tproffen/ORCSpilomar/circuitpython/tiny2350-tmc2209/pilomar/helpers.py

# Based on https://github.com/Short-bus/pilomar
# Simplified for use with TINY2350

import board
import digitalio
import time
import gc

#-----------------------------------------------------------------------------------------------
class GPIOpin():

    PinList = [] # Maintain a list of all defined pins.

    def __init__(self,pin,name=None):
        print("GPIOpin: Initializing pin",pin,name)
        self.Pin = digitalio.DigitalInOut(pin)
        self.PinNumber = pin
        self.Name = name
        self.PrevValue = self.GetValue()
        GPIOpin.PinList.append(self) # Add this pin to the list of defined pins.

    def SetDirection(self,direction):
        self.Pin.direction = direction
        if direction == digitalio.Direction.OUTPUT: self.Pin.value = False # turn off.

    def SetValue(self,value):
        if self.Pin.direction == digitalio.Direction.OUTPUT: self.Pin.value = value

    def GetValue(self):
        return self.Pin.value

    def High(self):
        return self.GetValue()

    def Low(self):
        return not self.GetValue()

    def Pressed(self):
        """ Return TRUE if the pin has just gone HIGH else FALSE. """
        result = False
        if self.Pin.value != self.PrevValue:
            if self.Pin.value: # Gone HIGH.
                result = True
            self.PrevValue = self.Pin.value
        return result

    def Released(self):
        """ Return TRUE if the pin has just gone LOW else FALSE. """
        result = False
        if self.Pin.value != self.PrevValue:
            if not self.Pin.value: # Gone LOW.
                result = True
            self.PrevValue = self.Pin.value
        return result

#-----------------------------------------------------------------------------------------------
class led():
    def __init__(self,pin,state=False):
        """ Tiny RGB LED on/off state is inverted!
            ie to turn LED ON, pin must go LOW.
               to turn LED OFF, pin must go HIGH. """
        self.Led = digitalio.DigitalInOut(pin)
        self.Led.direction = digitalio.Direction.OUTPUT
        self.Led.value = None # Off
        self.Enabled = True # Set to FALSE to turn off the LED completely.
        if state: self.On()
        else: self.Off()

    def Enable(self):
        """ Enable the LED and turn it on if required. """
        self.Enabled = True
        if self.Led.value: self.On()

    def Disable(self):
        """ Disable the LED and make sure it is turned off. """
        self.Enabled = False
        self.Off()

    def On(self):
        """ Turn the LED ON.
            NOTE: Tiny RGB LED uses opposite pin state to control LED. """
        if self.Enabled: self.Led.value = False
        else: self.Led.value = True

    def Off(self):
        """ Turn the LED OFF.
            NOTE: Tiny RGB LED uses opposite pin state to control LED. """
        self.Led.value = True

#-----------------------------------------------------------------------------------------------
class statusled():
    """ Pimoroni Tiny RGB LED version of RGB LED handling.
        The RGB LED is a collection of three led() objects. """
    def __init__(self):
        self.LedR = led(board.LED_R) # Create LED for RED channel.
        self.LedG = led(board.LED_G) # Create LED for GREEN channel.
        self.LedB = led(board.LED_B) # Create LED for BLUE channel.
        self.TaskList = {'idle': (False,False,False), # Off
                         'coms': (False,False,True), # Blue - Flashes when handling UART
                         'move': (False,True,False), # green - Flashes when motor is moving.
                         'error': (True,False,False), # Red - Indicates failure/fault.
                         'init': (False,True,True)} # cyan - System is initializing.
        self.Enabled = True # If set to FALSE, the LED is permanently off except for ERROR conditions.
        self.StatusExpiry = 0 # microsecond count when any error status can be cleared.
        self.Task('idle')

    def Enable(self):
        """ Enable the LED. """
        self.Enabled = True

    def Disable(self):
        """ Disable the LED. """
        self.Enabled = False
        self.Task('idle')

    def Task(self,task):
        """ Set LED color according to the task assigned.
            ERROR tasks always win, and an ERROR setting stays illuminated for at least 1 second
            before any other task can set any other colors. """
        ErrorTask = 'error'
        ms = int(time.monotonic_ns() / 1e9) # Seconds timer. Reduce by 1.0e9 to get seconds.
        if ms < self.StatusExpiry: # Error code is still valid. No other setting can be used yet.
            pass
        elif self.Enabled or task == ErrorTask: # No current ERROR status, so we can consider whether to set the new status.
            if task == ErrorTask: # Setting a new error status. Set the timeout for 1 second ahead.
                self.StatusExpiry = ms + 1 # Set 1 second expiry on error codes.
            if task in self.TaskList: # Pull the color codes for the selected task.
                t = self.TaskList[task]
                if t[0]: self.LedR.On()
                else: self.LedR.Off()
                if t[1]: self.LedG.On()
                else: self.LedG.Off()
                if t[2]: self.LedB.On()
                else: self.LedB.Off()
            else: # If the task is not recognised, the LEDs are turned off.
                self.LedR.Off()
                self.LedG.Off()
                self.LedB.Off()
        else: # LED is disabled for everything except ERRORS
            self.LedR.Off()
            self.LedG.Off()
            self.LedB.Off()

    def SetRGB(self,line):
        """ Receive a 'set rgb' command from the RPi and turn on
            the status LED in that color to acknowledge it.
            This is a debug/dev feature to let people prove that
            the Tiny is indeed receiving and processing commands.

            This works even if the LED is disabled!

            set rgb yyyymmddhhmmss y y y nnn
             0   1       2         3 4 5  6

            3 = y/n = RED ON
            4 = y/n = GREEN ON
            5 = y/n = BLUE ON
            6 = nnn = Minimum seconds to illuminate. """
        lineitems = line.split(' ')
        lli = len(lineitems)
        if lli > 3 and lineitems[3] == 'y': self.LedR.On()
        else: self.LedR.Off()
        if lli > 4 and lineitems[4] == 'y': self.LedG.On()
        else: self.LedG.Off()
        if lli > 5 and lineitems[5] == 'y': self.LedB.On()
        else: self.LedB.Off()
        if lli > 6:
            self.StatusExpiry = int(time.monotonic_ns() / 1e9) + int(lineitems[6]) # Set expiry on the LED color.# Write your code here :-)

#-----------------------------------------------------------------------------------------------
class exceptioncounter():
    """ Keep a count of how many exceptions have been raised during operation.
        All exceptions should be reported back to the RPi in the log messages
        however a simple counter also ensures we know when things are having
        problems. Implemented as a class so that it can be called consistently
        from inside other methods and objects.
        This will also automatically set the LED to the error color. """
    def __init__(self, StatusLed):
        self.StatusLed = StatusLed
        self.Count = 0 # Initialize the counter.

    def Reset(self):
        """ Reset the exception count. """
        self.Count = 0 # Initialize the counter.

    def Raise(self):
        try:
            self.Count += 1 # Increment the count.
            self.StatusLed.Task('error') # Set the LED to show an error was trapped.
            print("Exception trapped.")
        except Exception as e:
            print("exceptioncounter.Raise() failed:",str(e))

#-----------------------------------------------------------------------------------------------
class timer():
    """ An event timer mechanism.
        Create with
            NAME = timer('heartbeat',repeat=30,offset=10)
                'heartbeat' = name of the timer.
                repeat = 30 seconds between events.
                offset = 1st event is current time + 10 seconds.
        Use with
            if NAME.Due(): print ('Event due')

        This returns TRUE if the timer has expired.
        It automatically resets the timer to repeat.

        MyTimer = timer('demo',30)
        while True:
            if MyTimer.Due(): print("another 30 seconds has passed.")

        """

    def __init__(self,name,repeat,offset=0):
        """ Create the timer.
            Initialize the first due time. """
        self.Name = name
        if repeat < 1: repeat = 1 # Minimum repeat cycle is 1 second.
        self.RepeatSeconds = repeat
        if offset != 0: self.NextDue = time.time() + offset # If the timer starts with an offset then that's the FIRST due time.
        else: self.NextDue = time.time() + repeat # There's no offset, so due time is calculated from now.

    def SetNextDue(self):
        """ If NextDue has expired, this calculates the next future value.
            It always rolls forward a whole number of 'repeat seconds' to the first due time that is in the future. """
        while self.NextDue <= time.time():
            gap = ((time.time() - self.NextDue) // self.RepeatSeconds) + 1 # How many multiples of 'repeatseconds' do we need to add to get to the next timeslot?
            if gap >= 0:
                self.NextDue = self.NextDue + (self.RepeatSeconds * gap)

    def Reset(self):
        """ Restart the time from NOW. """
        self.NextDue = time.time() + self.RepeatSeconds

    def Remaining(self):
        """ How many seconds left on the timer? """
        remaining = self.NextDue - time.time()
        return remaining

    def Due(self):
        """ This returns TRUE if the timer has expired.
            It returns FALSE if the timer is still running.
            If the timer expires, it also resets the timer for the next event. """
        result = False
        temp = self.Remaining()
        if temp > self.RepeatSeconds: # If the local clock changes, the timer may be left out of sync. Reset it.
            print("clock(",self.Name,") remaining",temp,"exceeds repeat",self.RepeatSeconds,". Timer reset.")
            self.NextDue = time.time() + self.RepeatSeconds
        elif temp <= 0: # Timer expired.
            result = True
            self.SetNextDue()
        return result
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
